Scott216/Weather_Station_Data/Ethernet Lib/Ethernet.h

// Modified by SurferTim so different SS pins can be used
// See forum post: http://forum.arduino.cc/index.php?topic=217423.msg1601862#msg1601862


#ifndef ethernet_h
#define ethernet_h

#include <inttypes.h>
//#include "w5100.h"
#include "IPAddress.h"
#include "EthernetClient.h"
#include "EthernetServer.h"
#include "Dhcp.h"

#define MAX_SOCK_NUM 4

class EthernetClass {
private:
  IPAddress _dnsServerAddress;
  DhcpClass* _dhcp;
public:
  static uint8_t _state[MAX_SOCK_NUM];
  static uint16_t _server_port[MAX_SOCK_NUM];
  static uint8_t slaveSelect;
  // Initialise the Ethernet shield to use the provided MAC address and gain the rest of the
  // configuration through DHCP.
  // Returns 0 if the DHCP configuration failed, and 1 if it succeeded
  int begin(uint8_t *mac_address);
  void begin(uint8_t *mac_address, IPAddress local_ip);
  void begin(uint8_t *mac_address, IPAddress local_ip, IPAddress dns_server);
  void begin(uint8_t *mac_address, IPAddress local_ip, IPAddress dns_server, IPAddress gateway);
  void begin(uint8_t *mac_address, IPAddress local_ip, IPAddress dns_server, IPAddress gateway, IPAddress subnet);
  int maintain();
  void select(uint8_t _ss);
  
  IPAddress localIP();
  IPAddress subnetMask();
  IPAddress gatewayIP();
  IPAddress dnsServerIP();

  friend class EthernetClient;
  friend class EthernetServer;
};

extern EthernetClass Ethernet;

#endif
